gh0stless/SIDBlaster-USB-Tic-Tac-Edition/docs/images/2023-01-01_21-57-45.jpg

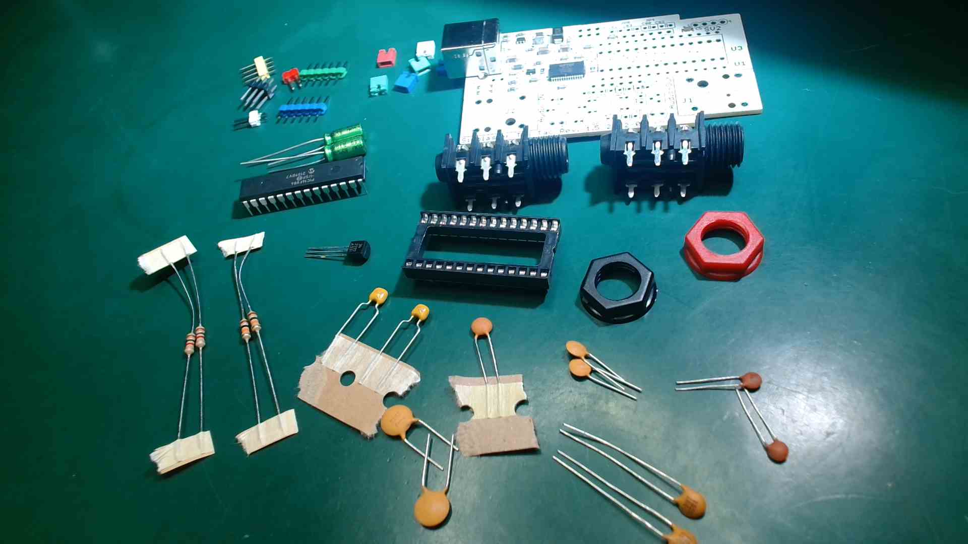
docs/images/2023-01-01_21-57-45.jpg
