gh0stless/SIDBlaster-USB-Tic-Tac-Edition/docs/images/2023-01-02_10-32-50.jpg

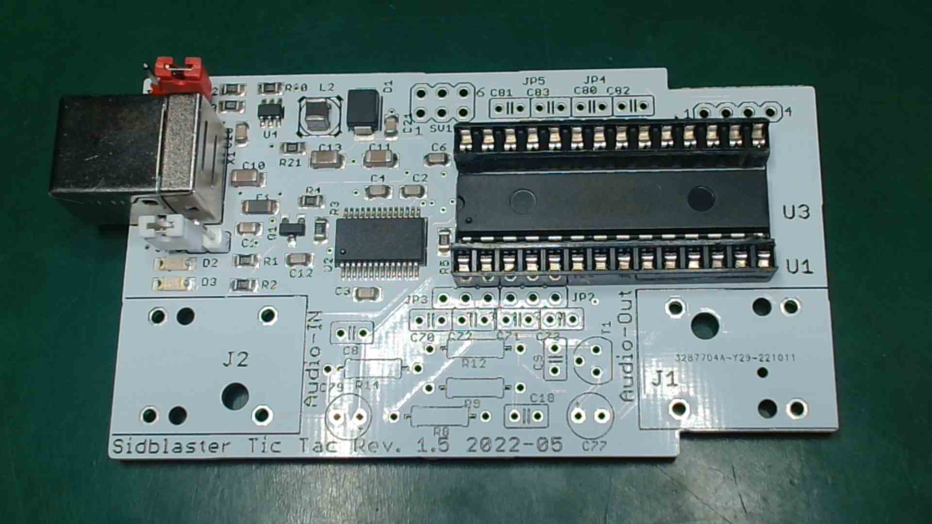
docs/images/2023-01-02_10-32-50.jpg
