gh0stless/SIDBlaster-USB-Tic-Tac-Edition/docs/images/2023-01-02_11-23-15.jpg

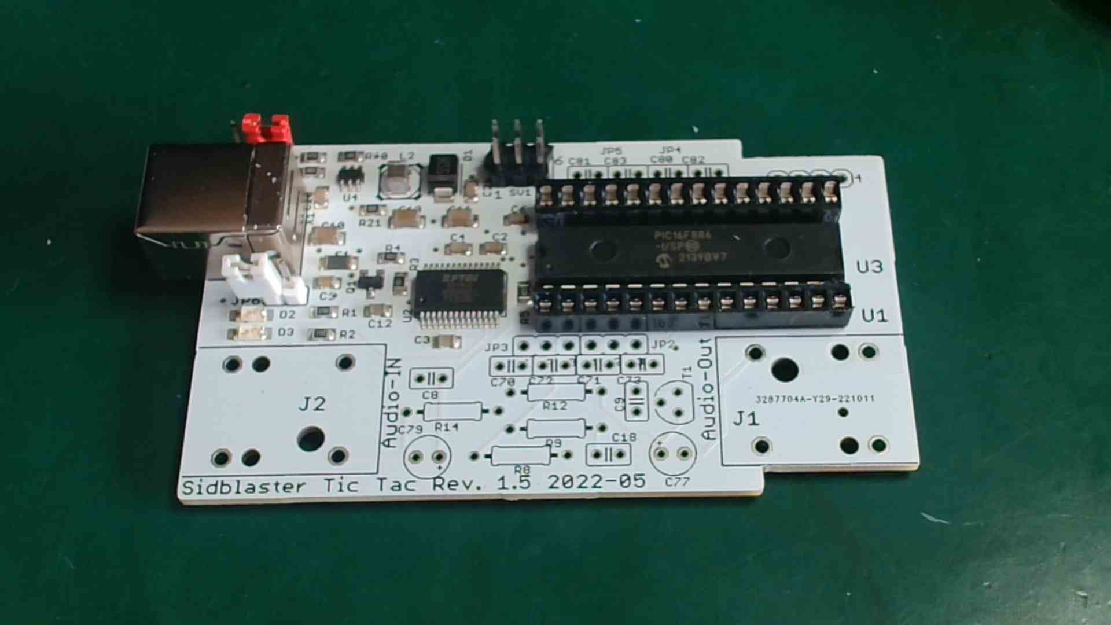
docs/images/2023-01-02_11-23-15.jpg
