gh0stless/SIDBlaster-USB-Tic-Tac-Edition/docs/images/2023-01-02_11-41-43.jpg

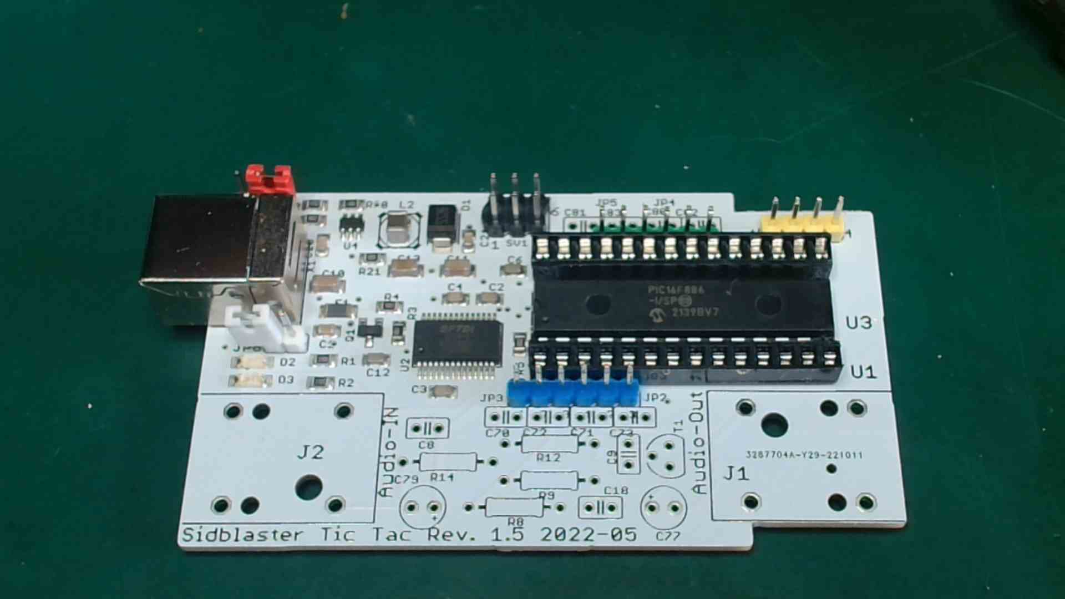
docs/images/2023-01-02_11-41-43.jpg
