gh0stless/SIDBlaster-USB-Tic-Tac-Edition/docs/images/2023-01-02_12-33-36.jpg

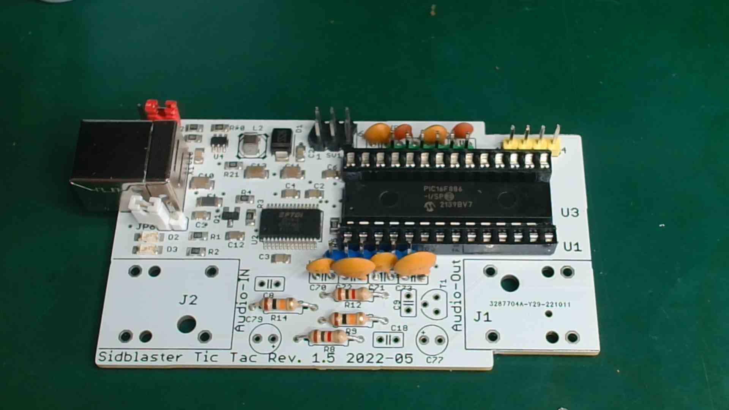
docs/images/2023-01-02_12-33-36.jpg
