gh0stless/SIDBlaster-USB-Tic-Tac-Edition/docs/images/2023-01-02_12-51-30.jpg

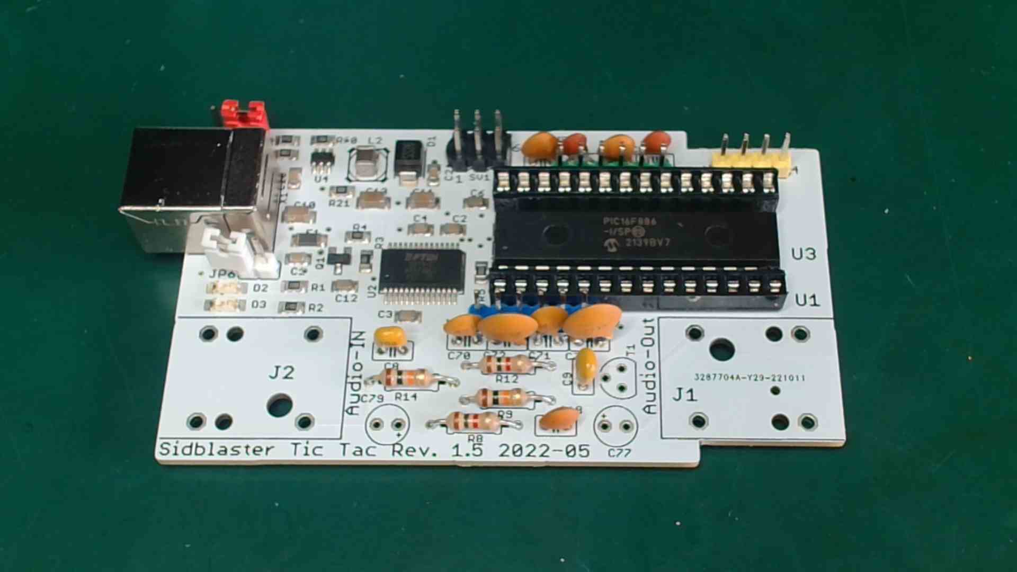
docs/images/2023-01-02_12-51-30.jpg
