gh0stless/SIDBlaster-USB-Tic-Tac-Edition/docs/images/2023-01-02_12-56-16.jpg

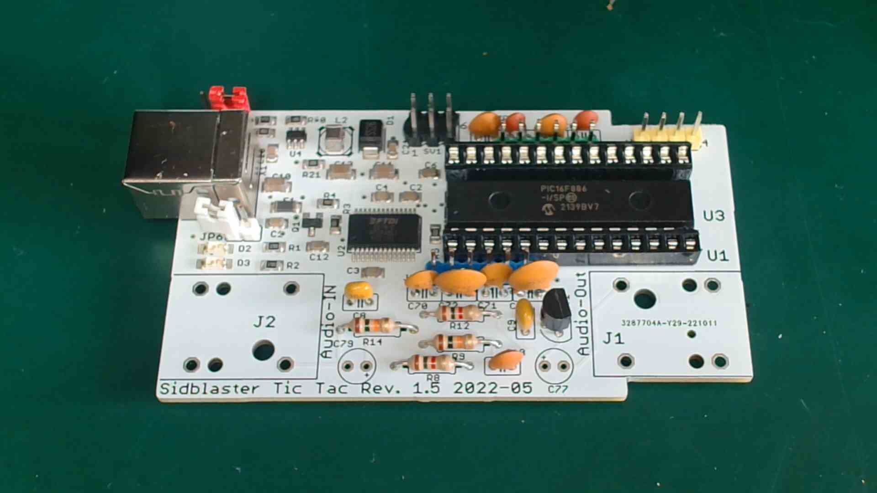
docs/images/2023-01-02_12-56-16.jpg
