gh0stless/SIDBlaster-USB-Tic-Tac-Edition/docs/images/2023-01-02_13-23-18.jpg

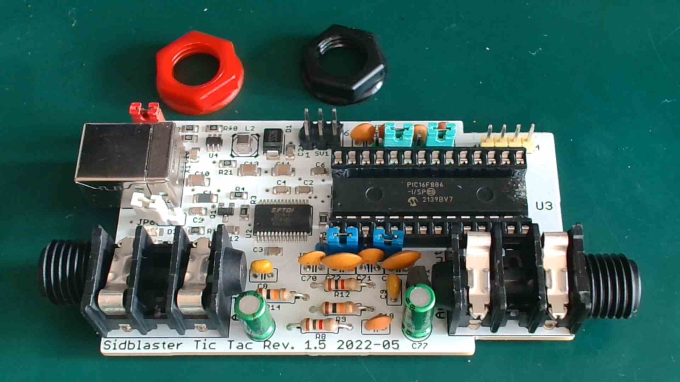
docs/images/2023-01-02_13-23-18.jpg
