gh0stless/SIDBlaster-USB-Tic-Tac-Edition/docs/images/20220504_162822-Mittel.jpg

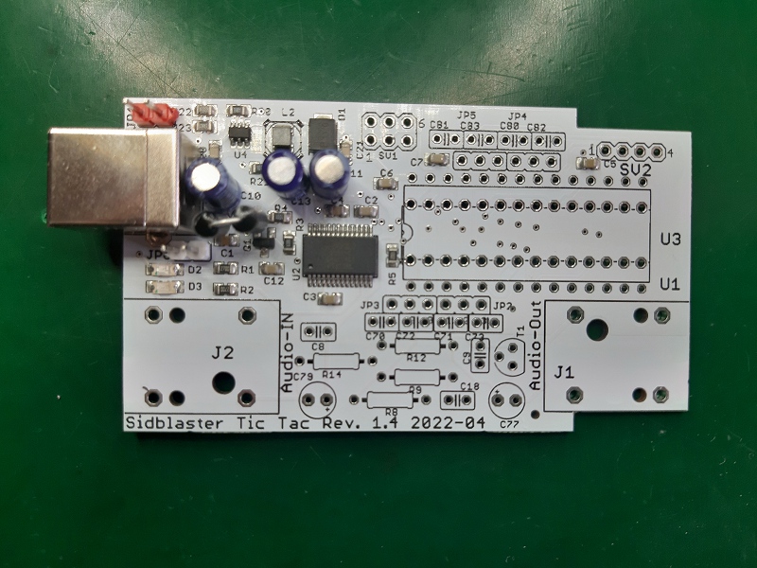
docs/images/20220504_162822-Mittel.jpg
