gh0stless/SIDBlaster-USB-Tic-Tac-Edition/docs/images/20220504_192443-Mittel.jpg

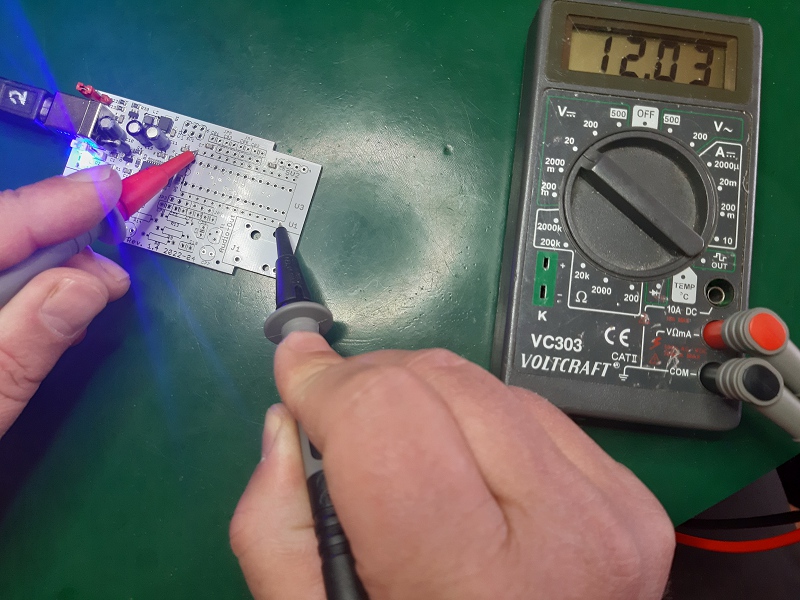
docs/images/20220504_192443-Mittel.jpg
