gh0stless/SIDBlaster-USB-Tic-Tac-Edition/docs/images/20220505_121421-Mittel.jpg

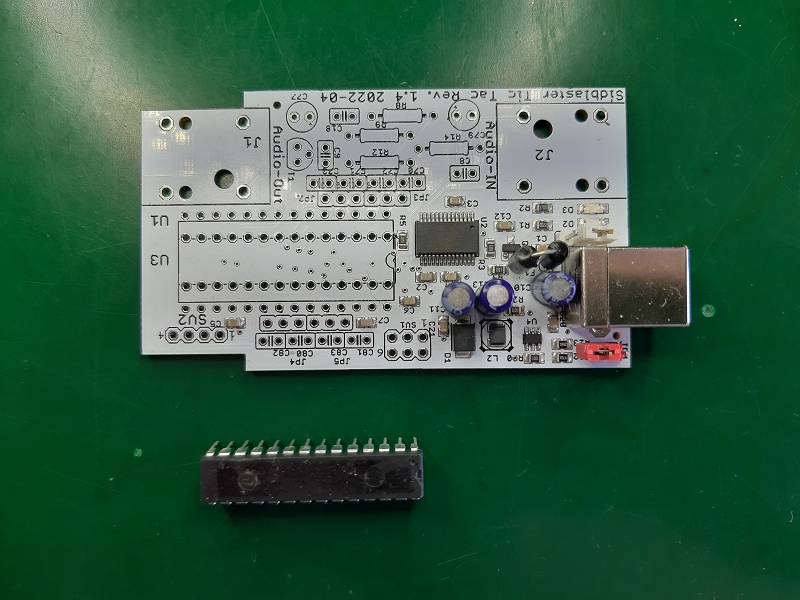
docs/images/20220505_121421-Mittel.jpg
