gh0stless/SIDBlaster-USB-Tic-Tac-Edition/docs/images/20220505_122357-Mittel.jpg

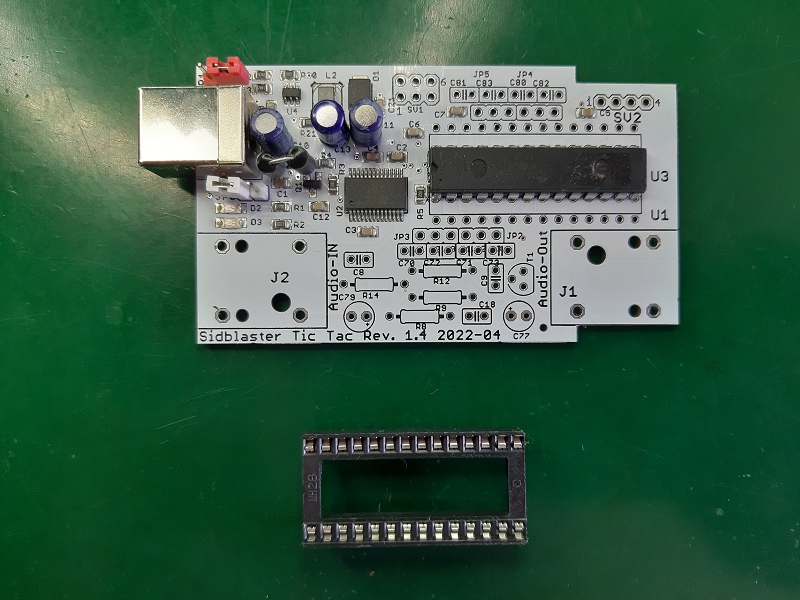
docs/images/20220505_122357-Mittel.jpg
