gh0stless/SIDBlaster-USB-Tic-Tac-Edition/docs/images/20220505_122702-Mittel.jpg

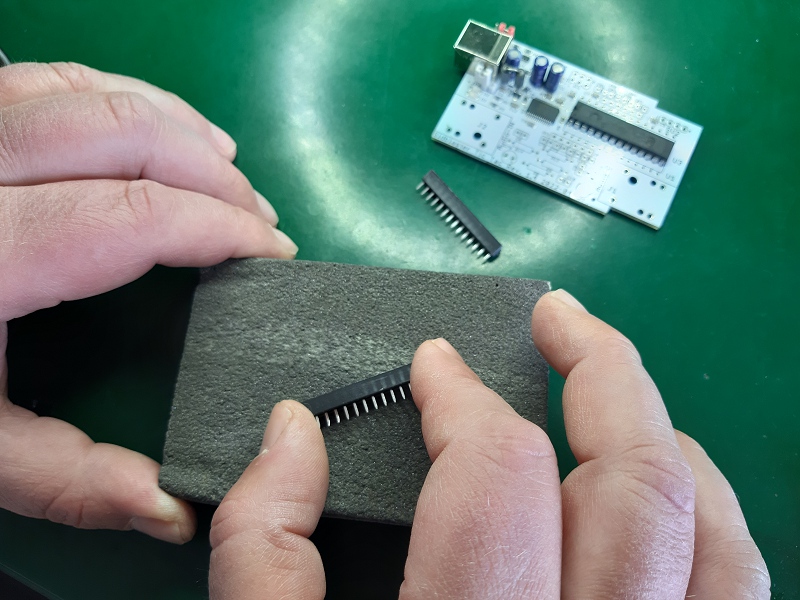
docs/images/20220505_122702-Mittel.jpg
