gh0stless/SIDBlaster-USB-Tic-Tac-Edition/docs/images/ACID64Player_2023-01-02_11-12-24.png

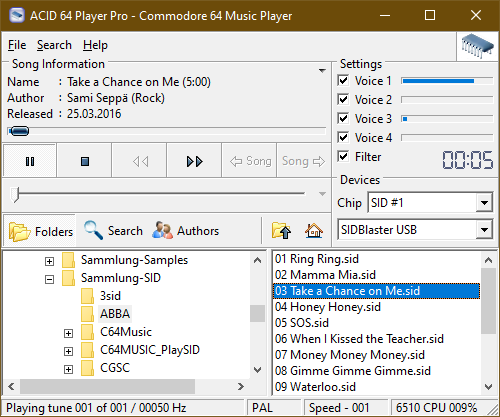
docs/images/ACID64Player_2023-01-02_11-12-24.png
