gh0stless/SIDBlaster-USB-Tic-Tac-Edition/docs/images/Picit3-SV1_photo.jpg

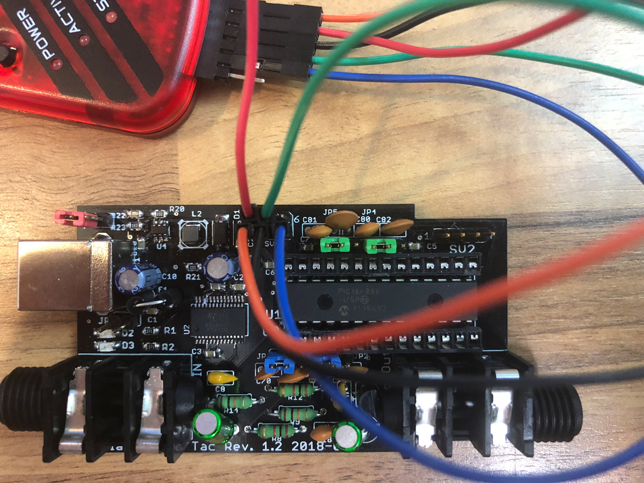
docs/images/Picit3-SV1_photo.jpg
