gh0stless/SIDBlaster-USB-Tic-Tac-Edition/exSIDBlaster/docs/exSIDBlaster_sch.png

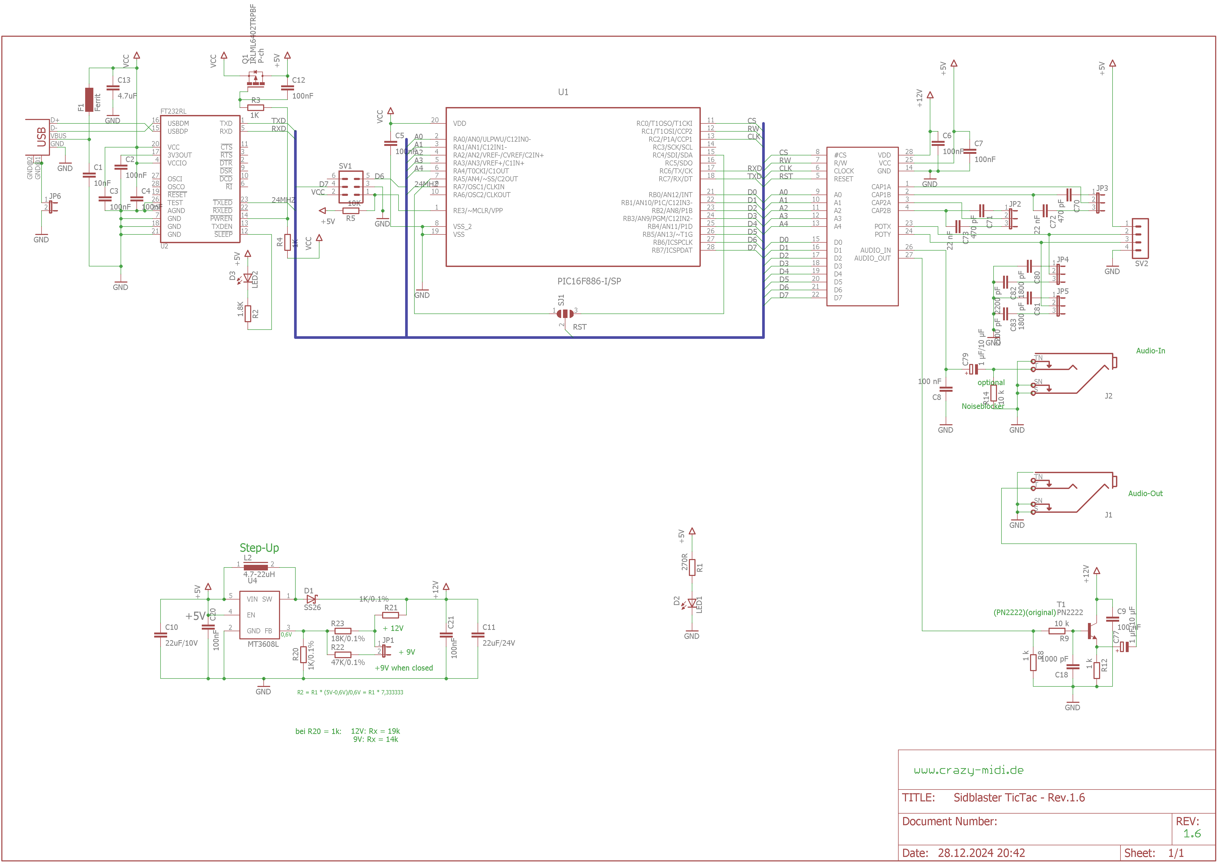
exSIDBlaster/docs/exSIDBlaster_sch.png
