gh0stless/SIDBlaster-USB-Tic-Tac-Edition/pcb/pcb_rev.1.5/Sidblaster_TicTac_-_Rev.1.5_pcb-all.png

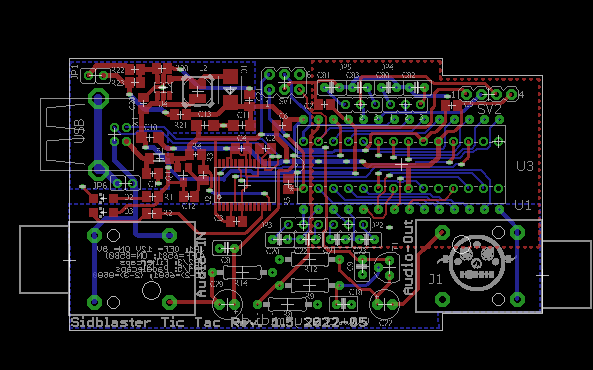
pcb/pcb_rev.1.5/Sidblaster_TicTac_-_Rev.1.5_pcb-all.png
